TinyCircuits/TinyCircuits-Whisker-Hall-Effect-AST1006/cad/Wireling_HALL_AST1006_REV2-DETAILED_DRAWING-PNG.png

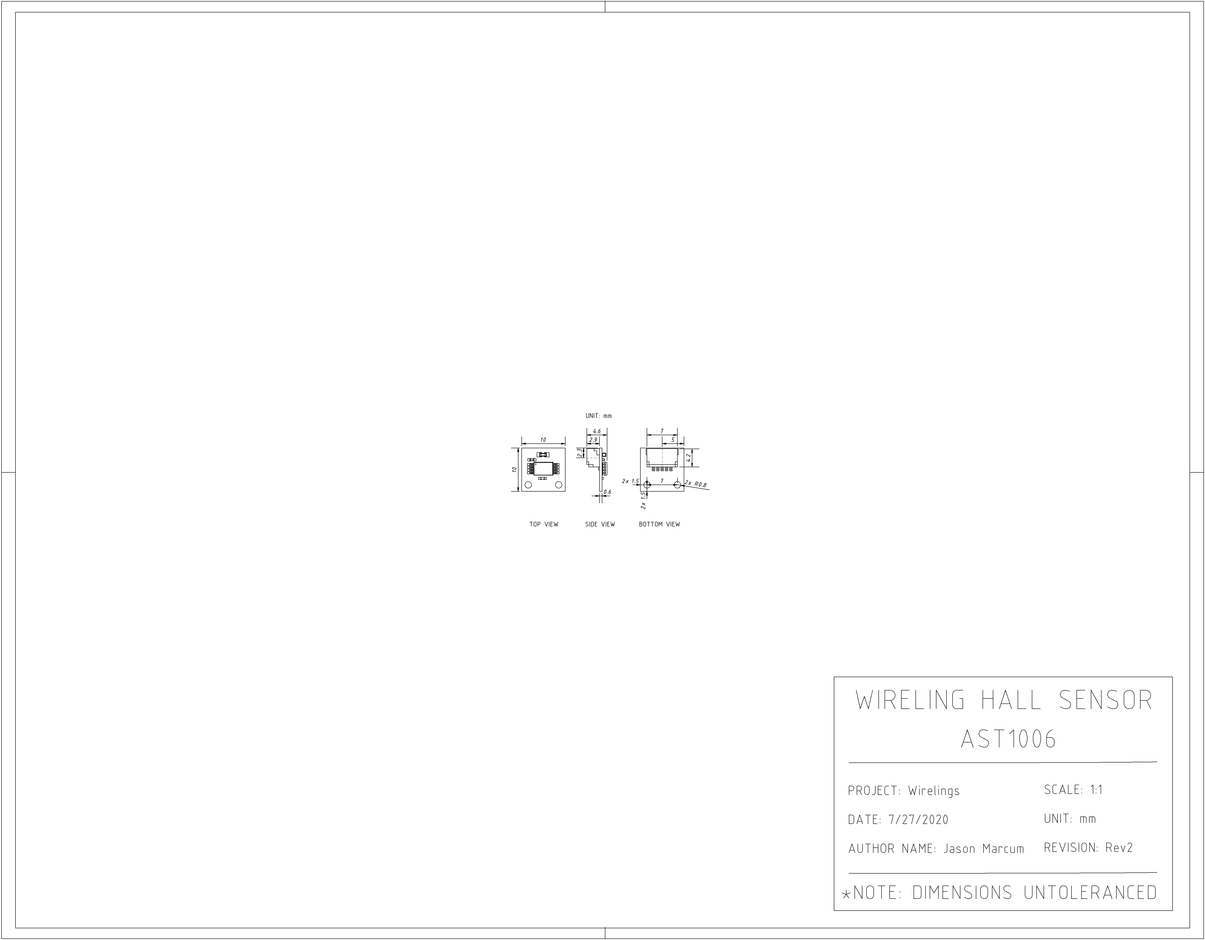
cad/Wireling_HALL_AST1006_REV2-DETAILED_DRAWING-PNG.png
