TinyCircuits/TinyCircuits-Whisker-Hall-Effect-AST1006/images/AST1006-A-Product-Photo-01.png

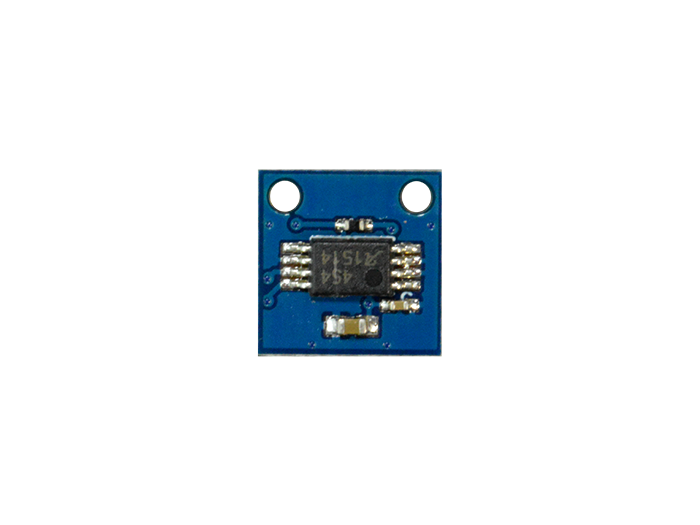
images/AST1006-A-Product-Photo-01.png
