TinyCircuits/TinyCircuits-Whisker-Hall-Effect-AST1006/images/AST1006-D-Learn-Photo-02.png

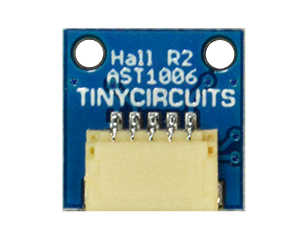
images/AST1006-D-Learn-Photo-02.png
