TinyCircuits/TinyCircuits-Whisker-Hall-Effect-AST1006/images/AST1006-A-Tutorial-Image-03.png

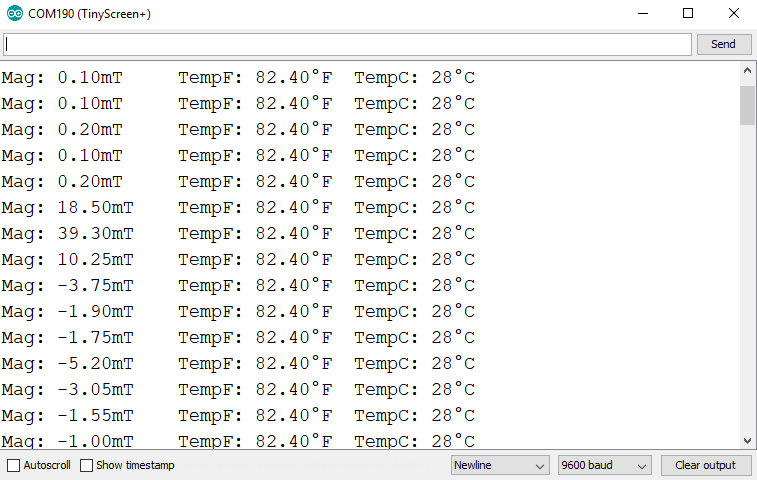
images/AST1006-A-Tutorial-Image-03.png
